rspg/usb_sound_card_with_pico/src/node.h

#pragma once

#include "debug.h"

namespace data_structure
{
    class node
    {
    public:
        node() = default;
        node(node* prev, node* next)
            : m_prev(prev)
            , m_next(next)
        {}

        void insert(node* where)
        {
            dbg_assert(where);
            dbg_assert(m_next==nullptr && m_prev==nullptr);

            m_prev = where;
            m_next = where->m_next;
            where->m_next->m_prev = this;
            where->m_next = this;
        }

        void remove()
        {
            if(m_next==nullptr && m_prev==nullptr)
                return;

            dbg_assert(m_next && m_prev);

            auto prev = m_prev;
            auto next = m_next;
            dbg_assert(prev->m_next == this);
            prev->m_next = next;
            dbg_assert(next->m_prev == this);
            next->m_prev = prev;

            m_next = nullptr;
            m_prev = nullptr;
        }

        node* prev() const { return m_prev; }
        node* next() const { return m_next; }

    private:
        node* m_prev = nullptr;
        node* m_next = nullptr;
    };

}
